kiu/rubylife/media/rubylife_kit_content_back.jpg

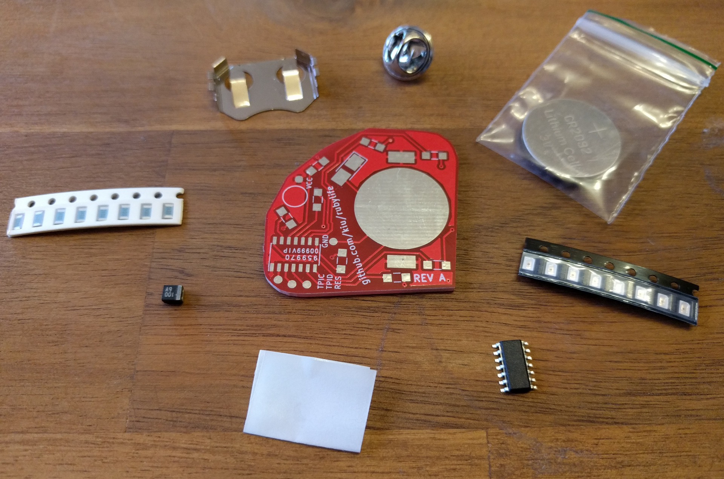
media/rubylife_kit_content_back.jpg
