kiu/rubylife/media/rubylife_kit_content_back_150x150.jpg

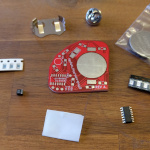
media/rubylife_kit_content_back_150x150.jpg
