kiu/rubylife/media/rubylife_kit_content_front_150x150.jpg

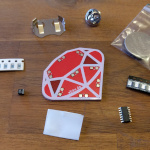
media/rubylife_kit_content_front_150x150.jpg
