kiu/rubylife/media/rubylife_kit_package.jpg

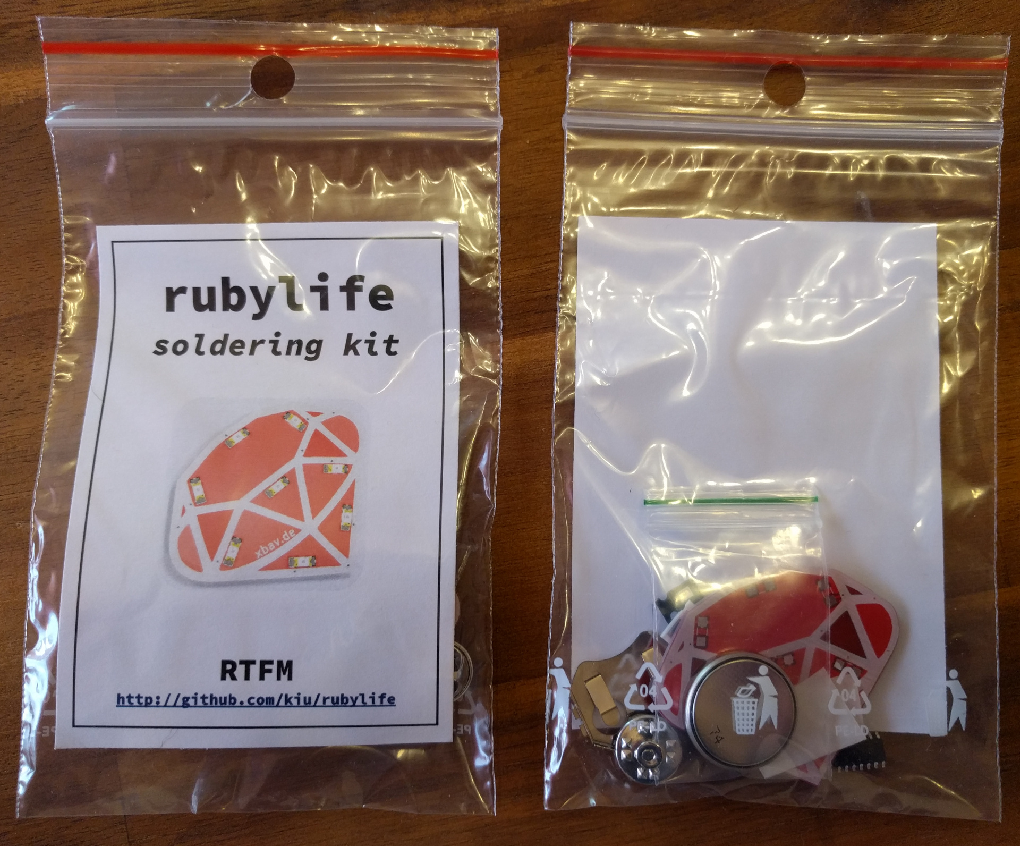
media/rubylife_kit_package.jpg
