kiu/rubylife/media/rubylife_kit_package_150x150.jpg

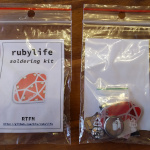
media/rubylife_kit_package_150x150.jpg
