kiu/rubylife/media/rubylife_kit_pile.jpg

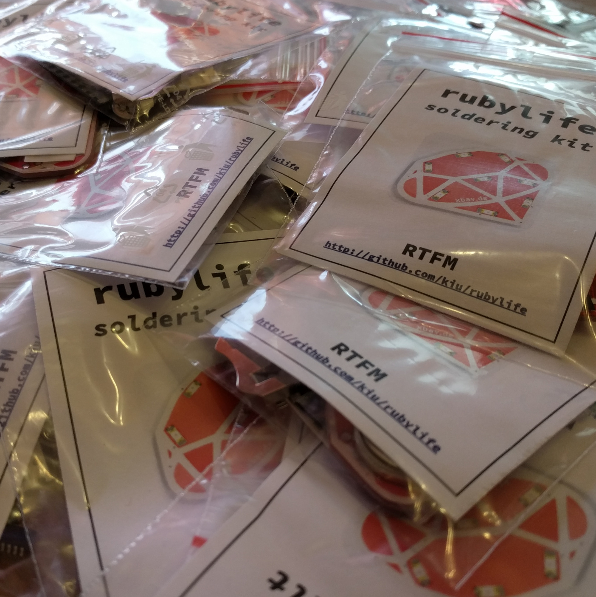
media/rubylife_kit_pile.jpg
