kiu/rubylife/media/rubylife_polarity_150x150.jpg

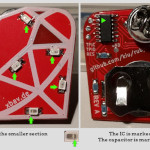
media/rubylife_polarity_150x150.jpg
