kiu/rubylife/media/rubylife_assembled.jpg

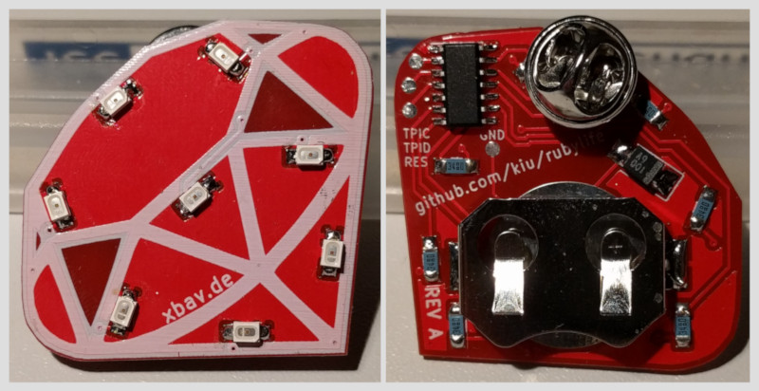
media/rubylife_assembled.jpg
