kiu/rubylife/media/rubylife_assembled_150x150.jpg

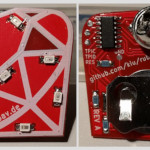
media/rubylife_assembled_150x150.jpg
